open-headset-interconnect-standard/collected-data/Audio Transformers/Data/EI-14 Blue TL003 1200:9/README.md

# Data for the EI-14 TL003, 1.2k:8

## CSV raw data

* [100mV](./Gain-Phase-THD-THDN-0.1v.csv)
* [300mV](./Gain-Phase-THD-THDN-0.3v.csv)
* [1V](./Gain-Phase-THD-THDN-1v.csv)
* [2V](./Gain-Phase-THD-THDN-2v.csv)
* [3V](./Gain-Phase-THD-THDN-3v.csv)
* [5V](./Gain-Phase-THD-THDN-5v.csv)

## Graphs

100mV:
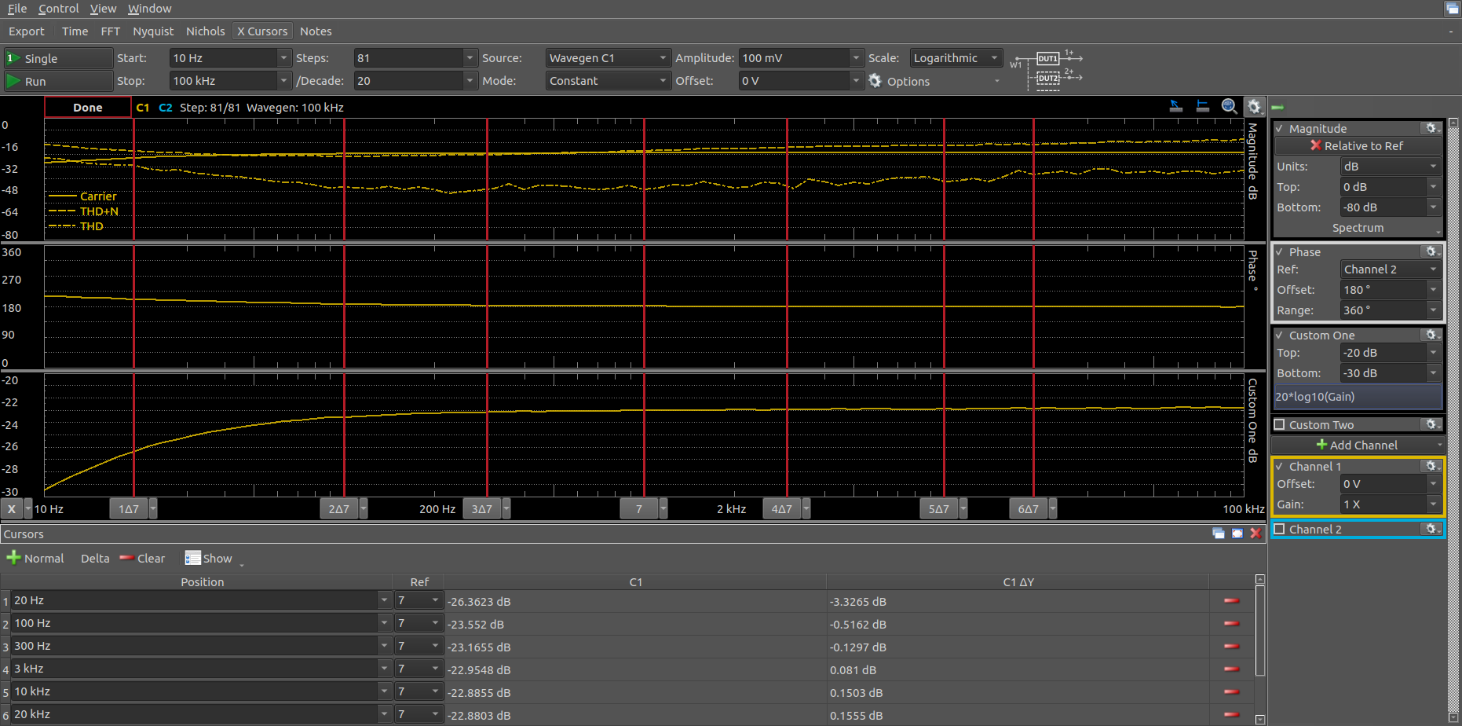
[picture p30: Audio Transformers/Data/EI-14 Blue TL003 1200:9/Gain-Phase-THD-THDN-0.1v.png]
100mV


300mV:
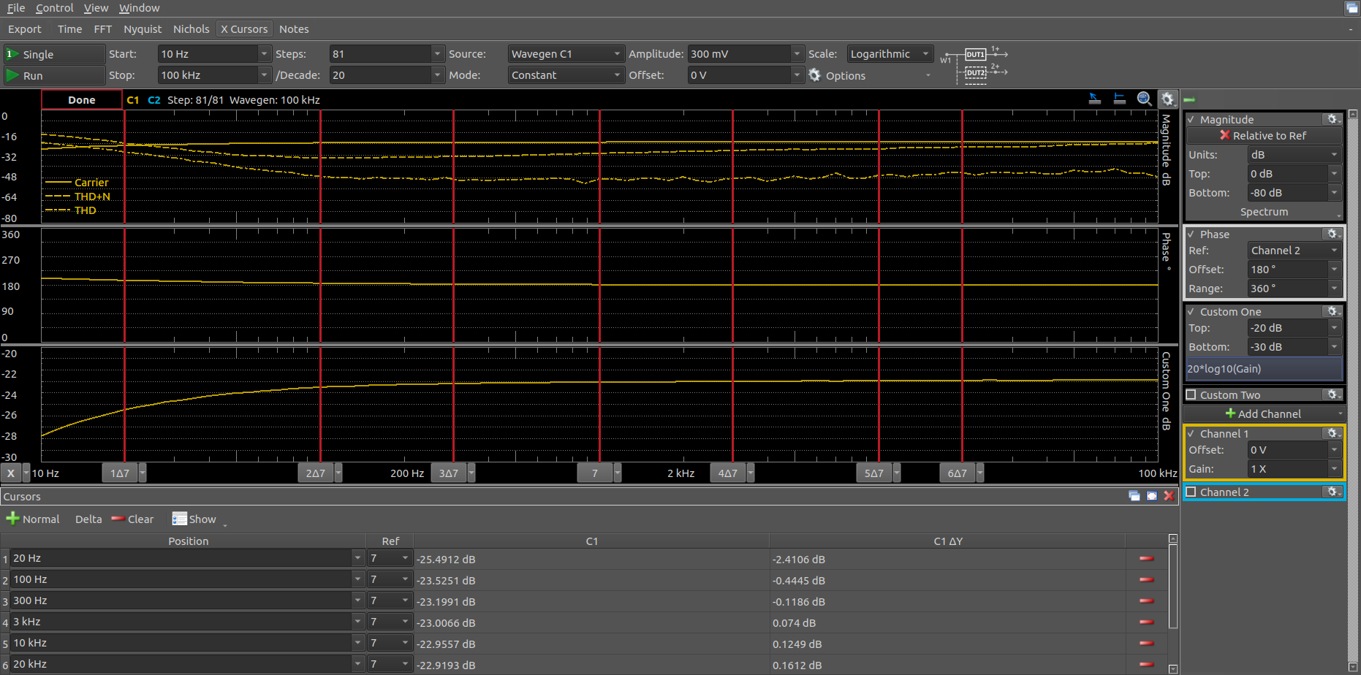
[picture p31: Audio Transformers/Data/EI-14 Blue TL003 1200:9/Gain-Phase-THD-THDN-0.3v.png]
300mV


1V:
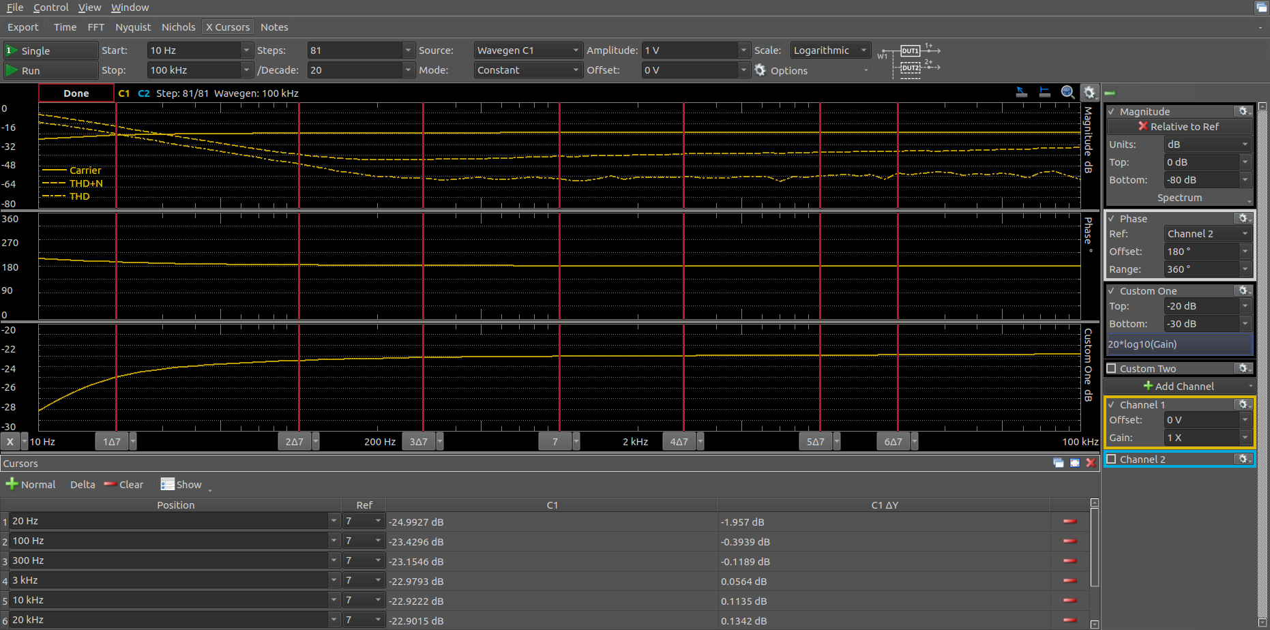
[picture p32: Audio Transformers/Data/EI-14 Blue TL003 1200:9/Gain-Phase-THD-THDN-1v.png]
1V


2V:
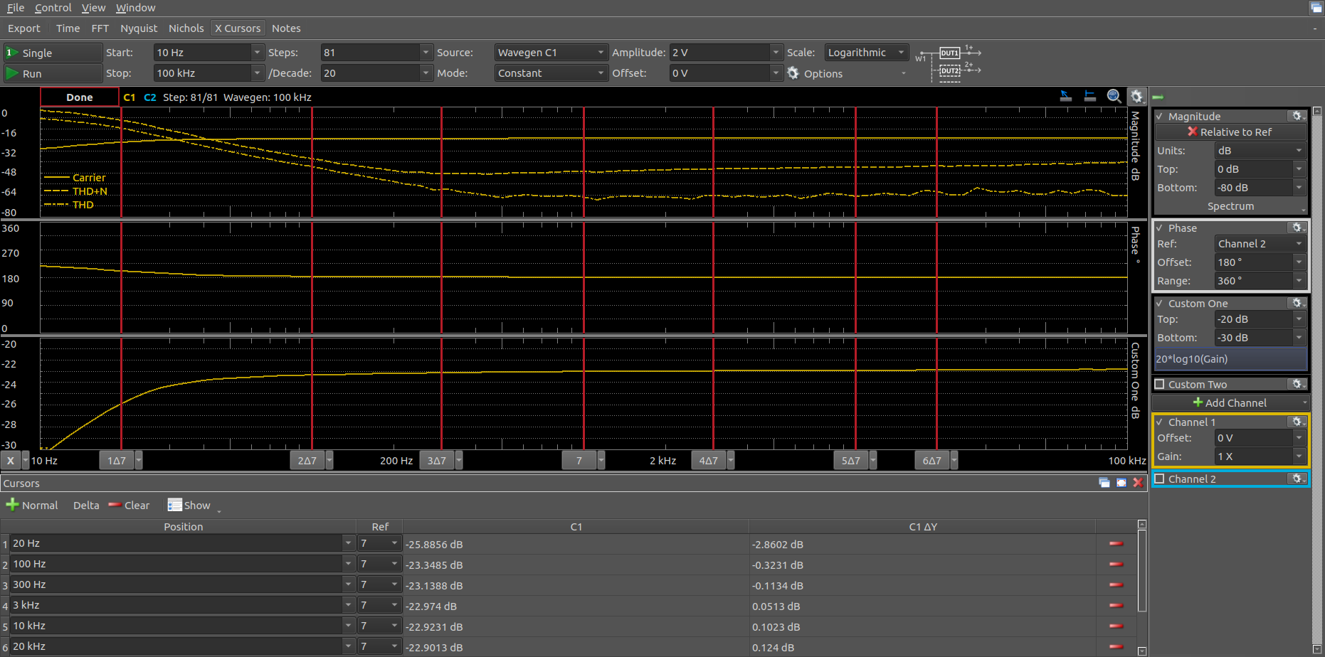
[picture p33: Audio Transformers/Data/EI-14 Blue TL003 1200:9/Gain-Phase-THD-THDN-2v.png]
2V


3V:
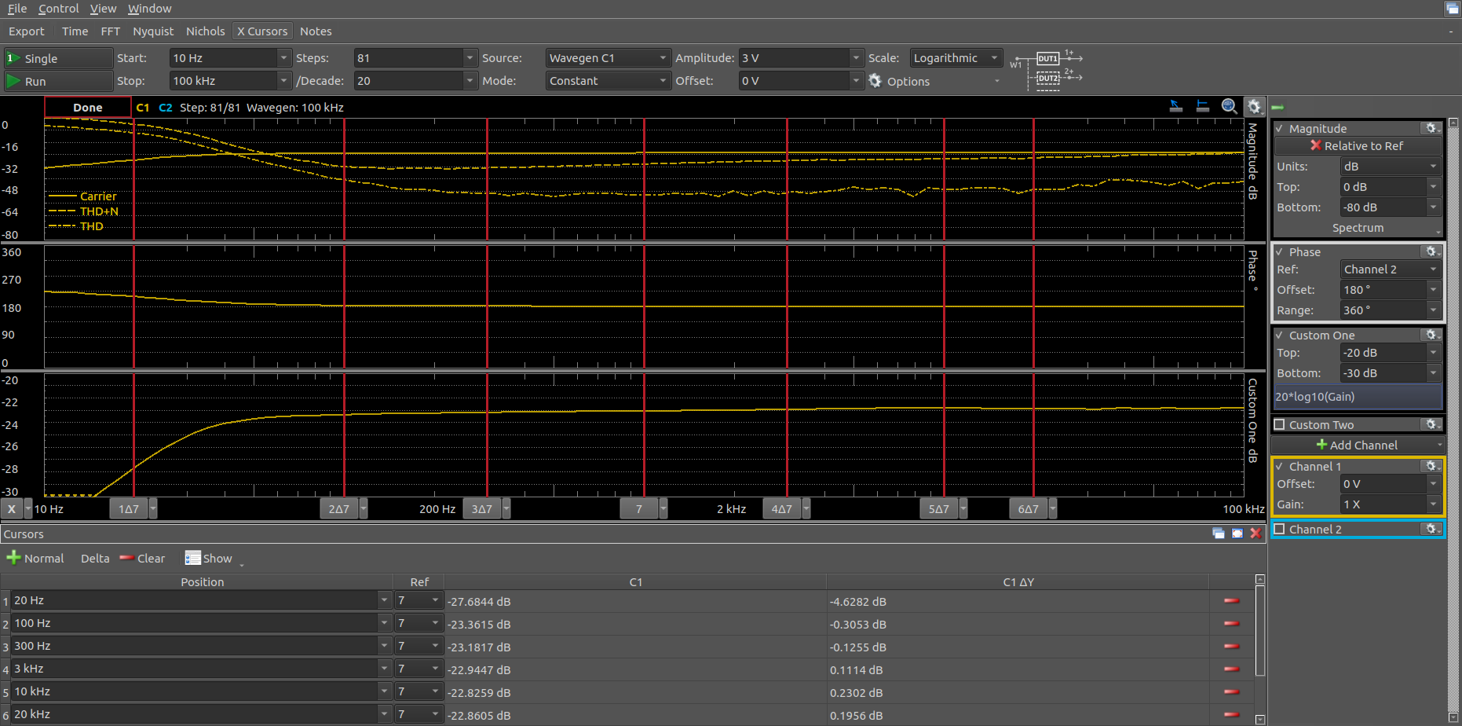
[picture p34: Audio Transformers/Data/EI-14 Blue TL003 1200:9/Gain-Phase-THD-THDN-3v.png]
3V


5V:
5V
