open-headset-interconnect-standard/collected-data/Audio Transformers/Data/PXSW PX-MB-CPE E-9818/README.md

# Data for the PXSW-PX-MB-CPE E-9818 from AliExpress

## CSV raw data

* [100mV](./Gain-Phase-THD-THDN-0.1v.csv)
* [300mV](./Gain-Phase-THD-THDN-0.3v.csv)
* [1V](./Gain-Phase-THD-THDN-1v.csv)
* [2V](./Gain-Phase-THD-THDN-2v.csv)
* [3V](./Gain-Phase-THD-THDN-3v.csv)
* [5V](./Gain-Phase-THD-THDN-5v.csv)

## Graphs

100mV:
100mV

300mV:
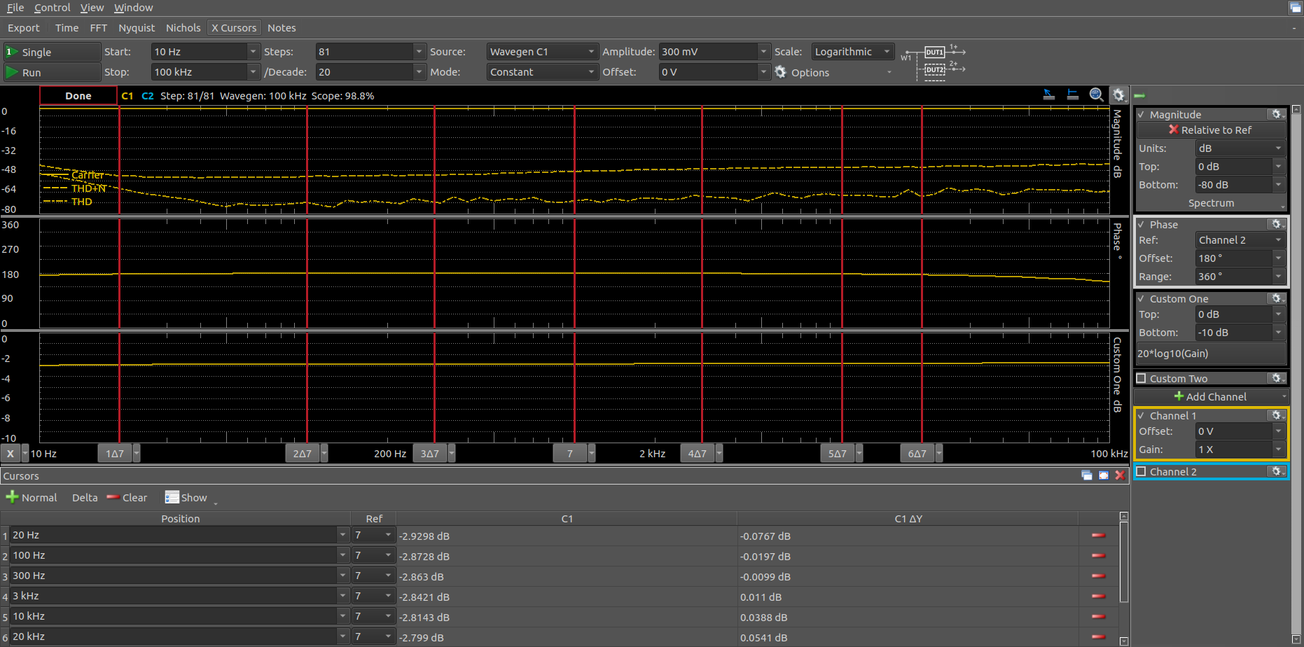
[picture p39: Audio Transformers/Data/PXSW PX-MB-CPE E-9818/Gain-Phase-THD-THDN-0.3v.png]
300mV


1V:
1V

2V:
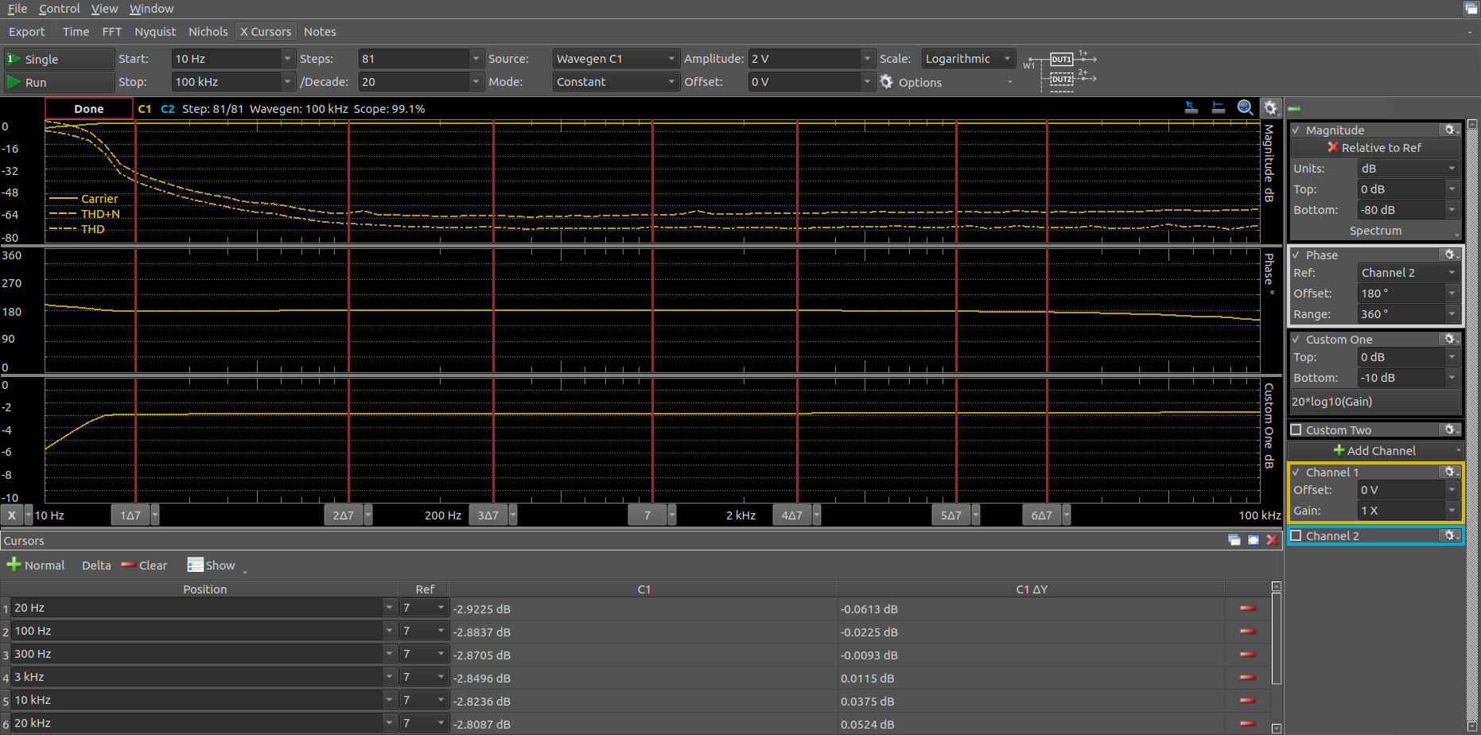
[picture p40: Audio Transformers/Data/PXSW PX-MB-CPE E-9818/Gain-Phase-THD-THDN-2v.png]
2V


3V:
3V

5V:
5V
