open-headset-interconnect-standard/collected-data/Audio Transformers/Data/Through Calibration/Gain-Phase-THD-THDN-1v.csv

#Digilent WaveForms Network Analyzer - Bode
#Device Name: Discovery2
#Serial Number: SN:210321A7F3E5
#Date Time: 2025-07-04 15:06:17.753
#Start: 10 Hz
#Stop: 100000 Hz
#Steps: 81
#Wavegen: Wavegen C1
#Amplification: 1 X
#Settle: 10 ms
#MinPeriods: 32
#Channel: Channel 1
#Range: 5.55283 V
#Offset: 0.000243159 V
#Relative: no
Frequency (Hz) | Channel 1 Magnitude (dB) | Channel 1 Magnitude THD+N (dB) | Channel 1 Magnitude THD (dB) | Channel 1 Phase (deg) | Channel 1 Custom One (dB)
10 | 0.02903148569005031 | -63.11874972781047 | -70.55348945358232 | -9.705146572005503 | 0.02903148569005031
11.22018454301963 | 0.02939541328029248 | -62.59853935174269 | -70.71674904282943 | -8.676447397927767 | 0.02939541328029248
12.589254117941675 | 0.029329812863790286 | -62.737042179514695 | -70.50430556199545 | -7.7536464664825075 | 0.029329812863790286
14.12537544622754 | 0.029258036078568014 | -62.635989019658595 | -70.44698647145728 | -6.927399331225203 | 0.029258036078568014
15.848931924611142 | 0.029265829220755064 | -60.04309397548501 | -70.24688894836741 | -6.187648509029849 | 0.029265829220755064
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
