open-headset-interconnect-standard/collected-data/Audio Transformers/Data/Through Calibration/Gain-Phase-THD-THDN-2v.csv

#Digilent WaveForms Network Analyzer - Bode
#Device Name: Discovery2
#Serial Number: SN:210321A7F3E5
#Date Time: 2025-07-04 15:06:51.911
#Start: 10 Hz
#Stop: 100000 Hz
#Steps: 81
#Wavegen: Wavegen C1
#Amplification: 1 X
#Settle: 10 ms
#MinPeriods: 32
#Channel: Channel 1
#Range: 5.55283 V
#Offset: 0.000243159 V
#Relative: no
Frequency (Hz) | Channel 1 Magnitude (dB) | Channel 1 Magnitude THD+N (dB) | Channel 1 Magnitude THD (dB) | Channel 1 Phase (deg) | Channel 1 Custom One (dB)
10 | 0.026525129940381566 | -66.88916893496085 | -73.9355812405627 | -9.614719198310688 | 0.026525129940381566
11.22018454301963 | 0.026625694199704193 | -65.50136713102133 | -73.92317922283554 | -8.603457222473082 | 0.026625694199704193
12.589254117941675 | 0.026605216985168677 | -66.45149991718141 | -73.81214127135817 | -7.694789127713129 | 0.026605216985168677
14.12537544622754 | 0.026688731914844013 | -66.35772701133065 | -73.75139093118366 | -6.879005567429459 | 0.026688731914844013
15.848931924611142 | 0.02679400495426679 | -61.72133480343576 | -73.80276952030734 | -6.147459676481546 | 0.02679400495426679
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
