open-headset-interconnect-standard/collected-data/Audio Transformers/Data/Through Calibration/Gain-Phase-THD-THDN-3v.csv

#Digilent WaveForms Network Analyzer - Bode
#Device Name: Discovery2
#Serial Number: SN:210321A7F3E5
#Date Time: 2025-07-04 15:07:25.658
#Start: 10 Hz
#Stop: 100000 Hz
#Steps: 81
#Wavegen: Wavegen C1
#Amplification: 1 X
#Settle: 10 ms
#MinPeriods: 32
#Channel: Channel 1
#Range: 61.0158 V
#Offset: -0.00262571 V
#Relative: no
Frequency (Hz) | Channel 1 Magnitude (dB) | Channel 1 Magnitude THD+N (dB) | Channel 1 Magnitude THD (dB) | Channel 1 Phase (deg) | Channel 1 Custom One (dB)
10 | 0.025148091906300643 | -57.01821924351933 | -72.01588805170464 | -9.528391111732212 | 0.025148091906300643
11.22018454301963 | 0.024997398266440297 | -57.21916099062909 | -71.52010305788276 | -8.528271124726814 | 0.024997398266440297
12.589254117941675 | 0.02482434211939763 | -57.426734789514605 | -72.55268147734637 | -7.636334824913755 | 0.02482434211939763
14.12537544622754 | 0.025579761158550575 | -57.302161962707856 | -73.05735765437821 | -6.83279898773975 | 0.025579761158550575
15.848931924611142 | 0.025183965894794345 | -56.300630537317424 | -72.57966029108901 | -6.106968917088345 | 0.025183965894794345
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
